menckow/Friendshiplamp/src/StandardCAs.h

#ifndef STANDARD_CAS_H
#define STANDARD_CAS_H

#include <Arduino.h>

/**
 * ISRG Root X1 - Standard Root Certificate for Let's Encrypt and HiveMQ.
 */
const char ISRG_ROOT_X1[] PROGMEM = R"rawliteral(
-----BEGIN CERTIFICATE-----
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
-----END CERTIFICATE-----
)rawliteral";

#endif
